rouming/FedorDesk/src/fedordesk.c

#include <string.h>

#include "fedordesk.h"

static led_state_t s_leds_state;

static void desk_clear_leds()
{
	hw_fire_leds_t cb = s_leds_state.hw_fire_leds;
	memset(&s_leds_state, 0, sizeof(s_leds_state));
	s_leds_state.hw_fire_leds = cb;
}

static void desk_fire_leds()
{
	// fire led
	for (uint8_t y = 0; y < BUTTONS_NUM; ++y) {
		if (s_leds_state.leds_matrix[y] != 0) {
			s_leds_state.hw_fire_leds(&s_leds_state.leds_matrix[y], y);
			return;
		}
	}
	// turn off
	s_leds_state.hw_fire_leds(&s_leds_state.leds_matrix[0], 0);
}

void desk_init_leds(hw_fire_leds_t cb)
{
	desk_clear_leds();
	s_leds_state.hw_fire_leds = cb;
}

button_t desk_button_pressed(button_t b)
{
	// pins jitter? ignore sequential presses in 500ms
	if (s_leds_state.timer_counter - s_leds_state.last_pressed_ms < 5)
		return s_leds_state.last_pressed_b;

	// set timer of button press
	s_leds_state.last_pressed_ms = s_leds_state.timer_counter;

	// increase speed or turn off
	// if button is the same
	if (s_leds_state.last_pressed_b == b) {
		// turn off leds if speed was the last
		if (s_leds_state.speed == led_speed2) {
			desk_clear_leds();
			// turn off
			desk_fire_leds();
		}
		// increase speed
		else
			++s_leds_state.speed;
	}
	// change mode
	else {
		// drop leds state
		memset(&s_leds_state.leds_matrix, 0, sizeof(s_leds_state.leds_matrix));
		// drop to initial speed
		s_leds_state.speed = led_speed0;
		// init button
		s_leds_state.last_pressed_b = b;

		// drop counters to change mode on next timer interrupt
		s_leds_state.timer_counter = 0;
		s_leds_state.last_pressed_ms = 0;
	}

	return s_leds_state.last_pressed_b;
}

void desk_timer_100ms_callback()
{
	uint8_t delay;
	switch (s_leds_state.speed) {
	case led_speed0:
		delay = 5; // 500 ms
		break;
	case led_speed1:
		delay = 3; // 300 ms
		break;
	case led_speed2:
		delay = 1; // 100 ms
		break;
	default:
		// unknown state
		return;
	}

	// check delay
	if (s_leds_state.timer_counter++ % delay != 0)
		return;

	switch (s_leds_state.last_pressed_b) {
	case button0:
		if (s_leds_state.leds_matrix[0] == 0)
			s_leds_state.leds_matrix[0] = (1 << (LEDS_NUM-1));
		else
			s_leds_state.leds_matrix[0] >>= 1;
		break;
	case button1:
		if (s_leds_state.leds_matrix[1] == 0)
			s_leds_state.leds_matrix[1] = 0b100100100100;
		else if (s_leds_state.leds_matrix[1] & 1)
			s_leds_state.leds_matrix[1] = 0;
		else
			s_leds_state.leds_matrix[1] >>= 1;
		break;
	case button2:
		if (s_leds_state.leds_matrix[0] == 0 &&
			s_leds_state.leds_matrix[1] == 0 &&
			s_leds_state.leds_matrix[2] == 0)
			s_leds_state.leds_matrix[2] = 0b111111111111;
		else if (s_leds_state.leds_matrix[0] == 0 &&
				 s_leds_state.leds_matrix[1] == 0 &&
				 s_leds_state.leds_matrix[2] != 0) {
			s_leds_state.leds_matrix[1] = 0b111111111111;
			s_leds_state.leds_matrix[2] = 0;
		}
		else if (s_leds_state.leds_matrix[0] == 0 &&
				 s_leds_state.leds_matrix[1] != 0 &&
				 s_leds_state.leds_matrix[2] == 0) {
			s_leds_state.leds_matrix[0] = 0b111111111111;
			s_leds_state.leds_matrix[1] = 0;
		}
		else if (s_leds_state.leds_matrix[0] != 0 &&
				 s_leds_state.leds_matrix[1] == 0 &&
				 s_leds_state.leds_matrix[2] == 0) {
			s_leds_state.leds_matrix[0] = 0;
		}
		break;
	default:
		// unknown state
		return;
	}

	// fire leds
	desk_fire_leds();
}
